ConstStrings/GoWinSDR/Firmware/GoWinSDR_STM32/Hardware/ad9361/command.c

/**************************************************************************//**
 *   @file   command.c
 *   @brief  Implementation of AD9361 Command Driver.
 *   @author DBogdan (dragos.bogdan@analog.com)
 *******************************************************************************
 * Copyright 2013(c) Analog Devices, Inc.
 *
 * All rights reserved.
 *
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
 * THIS SOFTWARE IS PROVIDED BY ANALOG DEVICES "AS IS" AND ANY EXPRESS OR
 * IMPLIED WARRANTIES, INCLUDING, BUT NOT LIMITED TO, NON-INFRINGEMENT,
 * MERCHANTABILITY AND FITNESS FOR A PARTICULAR PURPOSE ARE DISCLAIMED.
 * IN NO EVENT SHALL ANALOG DEVICES BE LIABLE FOR ANY DIRECT, INDIRECT,
 * INCIDENTAL, SPECIAL, EXEMPLARY, OR CONSEQUENTIAL DAMAGES (INCLUDING, BUT NOT
 * LIMITED TO, INTELLECTUAL PROPERTY RIGHTS, PROCUREMENT OF SUBSTITUTE GOODS OR
 * SERVICES; LOSS OF USE, DATA, OR PROFITS; OR BUSINESS INTERRUPTION) HOWEVER
 * CAUSED AND ON ANY THEORY OF LIABILITY, WHETHER IN CONTRACT, STRICT LIABILITY,
 * OR TORT (INCLUDING NEGLIGENCE OR OTHERWISE) ARISING IN ANY WAY OUT OF THE USE
 * OF THIS SOFTWARE, EVEN IF ADVISED OF THE POSSIBILITY OF SUCH DAMAGE.
*******************************************************************************/

/******************************************************************************/
/***************************** Include Files **********************************/
/******************************************************************************/
#include "command.h"
#include "console.h"
#include "ad9361_api.h"
#include "dac_core.h"
#include "com_fpga.h"

/******************************************************************************/
/************************ Constants Definitions *******************************/
/******************************************************************************/
command cmd_list[] = {
	{"help?", "Displays all available commands.", "", get_help},
	{"register?", "Gets the specified register value.", "", get_register},
	{"tx_lo_freq?", "Gets current TX LO frequency [MHz].", "", get_tx_lo_freq},
	{"tx_lo_freq=", "Sets the TX LO frequency [MHz].", "", set_tx_lo_freq},
	{"tx_samp_freq?", "Gets current TX sampling frequency [Hz].", "", get_tx_samp_freq},
	{"tx_samp_freq=", "Sets the TX sampling frequency [Hz].", "", set_tx_samp_freq},
	{"tx_rf_bandwidth?", "Gets current TX RF bandwidth [Hz].", "", get_tx_rf_bandwidth},
	{"tx_rf_bandwidth=", "Sets the TX RF bandwidth [Hz].", "", set_tx_rf_bandwidth},
	{"tx1_attenuation?", "Gets current TX1 attenuation [mdB].", "", get_tx1_attenuation},
	{"tx1_attenuation=", "Sets the TX1 attenuation [mdB].", "", set_tx1_attenuation},
	{"tx2_attenuation?", "Gets current TX2 attenuation [mdB].", "", get_tx2_attenuation},
	{"tx2_attenuation=", "Sets the TX2 attenuation [mdB].", "", set_tx2_attenuation},
	{"tx_fir_en?", "Gets current TX FIR state.", "", get_tx_fir_en},
	{"tx_fir_en=", "Sets the TX FIR state.", "", set_tx_fir_en},
	{"rx_lo_freq?", "Gets current RX LO frequency [MHz].", "", get_rx_lo_freq},
	{"rx_lo_freq=", "Sets the RX LO frequency [MHz].", "", set_rx_lo_freq},
	{"rx_samp_freq?", "Gets current RX sampling frequency [Hz].", "", get_rx_samp_freq},
	{"rx_samp_freq=", "Sets the RX sampling frequency [Hz].", "", set_rx_samp_freq},
	{"rx_rf_bandwidth?", "Gets current RX RF bandwidth [Hz].", "", get_rx_rf_bandwidth},
	{"rx_rf_bandwidth=", "Sets the RX RF bandwidth [Hz].", "", set_rx_rf_bandwidth},
	{"rx1_gc_mode?", "Gets current RX1 GC mode.", "", get_rx1_gc_mode},
	{"rx1_gc_mode=", "Sets the RX1 GC mode.", "", set_rx1_gc_mode},
	{"rx2_gc_mode?", "Gets current RX2 GC mode.", "", get_rx2_gc_mode},
	{"rx2_gc_mode=", "Sets the RX2 GC mode.", "", set_rx2_gc_mode},
	{"rx1_rf_gain?", "Gets current RX1 RF gain.", "", get_rx1_rf_gain},
	{"rx1_rf_gain=", "Sets the RX1 RF gain.", "", set_rx1_rf_gain},
	{"rx2_rf_gain?", "Gets current RX2 RF gain.", "", get_rx2_rf_gain},
	{"rx2_rf_gain=", "Sets the RX2 RF gain.", "", set_rx2_rf_gain},
	{"rx_fir_en?", "Gets current RX FIR state.", "", get_rx_fir_en},
	{"rx_fir_en=", "Sets the RX FIR state.", "", set_rx_fir_en},
	{"dds_tx1_tone1_freq?", "Gets current DDS TX1 Tone 1 frequency [Hz].", "", get_dds_tx1_tone1_freq},
	{"dds_tx1_tone1_freq=", "Sets the DDS TX1 Tone 1 frequency [Hz].", "", set_dds_tx1_tone1_freq},
	{"dds_tx1_tone2_freq?", "Gets current DDS TX1 Tone 2 frequency [Hz].", "", get_dds_tx1_tone2_freq},
	{"dds_tx1_tone2_freq=", "Sets the DDS TX1 Tone 2 frequency [Hz].", "", set_dds_tx1_tone2_freq},
	{"dds_tx1_tone1_phase?", "Gets current DDS TX1 Tone 1 phase [degrees].", "", get_dds_tx1_tone1_phase},
	{"dds_tx1_tone1_phase=", "Sets the DDS TX1 Tone 1 phase [degrees].", "", set_dds_tx1_tone1_phase},
	{"dds_tx1_tone2_phase?", "Gets current DDS TX1 Tone 2 phase [degrees].", "", get_dds_tx1_tone2_phase},
	{"dds_tx1_tone2_phase=", "Sets the DDS TX1 Tone 2 phase [degrees].", "", set_dds_tx1_tone2_phase},
	{"dds_tx1_tone1_scale?", "Gets current DDS TX1 Tone 1 scale.", "", get_dds_tx1_tone1_scale},
	{"dds_tx1_tone1_scale=", "Sets the DDS TX1 Tone 1 scale.", "", set_dds_tx1_tone1_scale},
	{"dds_tx1_tone2_scale?", "Gets current DDS TX1 Tone 2 scale.", "", get_dds_tx1_tone2_scale},
	{"dds_tx1_tone2_scale=", "Sets the DDS TX1 Tone 2 scale.", "", set_dds_tx1_tone2_scale},
	{"dds_tx2_tone1_freq?", "Gets current DDS TX2 Tone 1 frequency [Hz].", "", get_dds_tx2_tone1_freq},
	{"dds_tx2_tone1_freq=", "Sets the DDS TX2 Tone 1 frequency [Hz].", "", set_dds_tx2_tone1_freq},
	{"dds_tx2_tone2_freq?", "Gets current DDS TX2 Tone 2 frequency [Hz].", "", get_dds_tx2_tone2_freq},
	{"dds_tx2_tone2_freq=", "Sets the DDS TX2 Tone 2 frequency [Hz].", "", set_dds_tx2_tone2_freq},
	{"dds_tx2_tone1_phase?", "Gets current DDS TX2 Tone 1 phase [degrees].", "", get_dds_tx2_tone1_phase},
	{"dds_tx2_tone1_phase=", "Sets the DDS TX2 Tone 1 phase [degrees].", "", set_dds_tx2_tone1_phase},
	{"dds_tx2_tone2_phase?", "Gets current DDS TX2 Tone 2 phase [degrees].", "", get_dds_tx2_tone2_phase},
	{"dds_tx2_tone2_phase=", "Sets the DDS TX2 Tone 2 phase [degrees].", "", set_dds_tx2_tone2_phase},
	{"dds_tx2_tone1_scale?", "Gets current DDS TX2 Tone 1 scale.", "", get_dds_tx2_tone1_scale},
	{"dds_tx2_tone1_scale=", "Sets the DDS TX2 Tone 1 scale.", "", set_dds_tx2_tone1_scale},
	{"dds_tx2_tone2_scale?", "Gets current DDS TX2 Tone 2 scale.", "", dds_tx2_tone2_scale},
	{"dds_tx2_tone2_scale=", "Sets the DDS TX2 Tone 2 scale.", "", set_dds_tx2_tone2_scale},
	{"calibration?", "Get Lo Freq diff.","", get_lo_diff},
	{"calibration=", "Calibrate Lo Freq diff.","", cal_lo_diff},
	{"rx_lo_up=", "Increase RX LO frequency.","", rx_lo_up},
	{"rx_lo_down=", "Decrease RX LO frequency.","", rx_lo_down},
	{"query_led_state?", "Decrease RX LO frequency.","", query_led_state},
	{"query_led_state=", "Decrease RX LO frequency.","", query_led_state_set},
	{"query_temp?", "Get Board Temperature.","", query_temp},
	{"fan_state_set=", "Set fan enable.","", fan_state_set},
};
const char cmd_no = (sizeof(cmd_list) / sizeof(command));

/******************************************************************************/
/************************ Variables Definitions *******************************/
/******************************************************************************/
extern struct dds_state dds_st;
extern struct ad9361_rf_phy *ad9361_phy;

/**************************************************************************//***
 * @brief Show the invalid parameter message.
 *
 * @return None.
*******************************************************************************/
void show_invalid_param_message(unsigned char cmd_no)
{
	console_print("Invalid parameter!\n");
	console_print("%s  - %s\n", (char*)cmd_list[cmd_no].name, (char*)cmd_list[cmd_no].description);
	console_print("Example: %s\n", (char*)cmd_list[cmd_no].example);
}

/**************************************************************************//***
 * @brief Displays all available commands.
 *
 * @return None.
*******************************************************************************/
void get_help(double* param, char param_no) // "help?" command
{
	unsigned char display_cmd;

	console_print("Available commands:\n");
	for(display_cmd = 0; display_cmd < cmd_no; display_cmd++)
	{
		console_print("%s  - %s\n", (char*)cmd_list[display_cmd].name,
								  (char*)cmd_list[display_cmd].description);
	}
}

/**************************************************************************//***
 * @brief Displays all available commands.
 *
 * @return None.
*******************************************************************************/
void get_register(double* param, char param_no) // "register?" command
{
	// uint16_t reg_addr;
	// uint8_t reg_val;
	// SPI_HandleTypeDef spi;

	// if(param_no >= 1)
	// {
	// 	spi.id_no = 0;
	// 	reg_addr = param[0];
	// 	reg_val = ad9361_spi_read(&spi, reg_addr);
	// 	console_print("register[0x%x]=0x%x\n", reg_addr, reg_val);
	// }
	// else
	// 	show_invalid_param_message(1);
	console_print("Use empty: command.c::get_register\n");
}

/**************************************************************************//***
 * @brief Gets current TX LO frequency [MHz].
 *
 * @return None.
*******************************************************************************/
void get_tx_lo_freq(double* param, char param_no) // "tx_lo_freq?" command
{
	uint64_t lo_freq_hz;

	ad9361_get_tx_lo_freq(ad9361_phy, &lo_freq_hz);
	lo_freq_hz /= 1000000;
	console_print("tx_lo_freq=%d\n", (uint32_t)lo_freq_hz);
}

/**************************************************************************//***
 * @brief Sets the TX LO frequency [MHz].
 *
 * @return None.
*******************************************************************************/
void set_tx_lo_freq(double* param, char param_no) // "tx_lo_freq=" command
{
	uint64_t lo_freq_hz;

	if(param_no >= 1)
	{
		lo_freq_hz = param[0];
		lo_freq_hz *= 1000000;
		ad9361_set_tx_lo_freq(ad9361_phy, lo_freq_hz);
		lo_freq_hz /= 1000000;
		console_print("tx_lo_freq=%d\n", (uint32_t)lo_freq_hz);
	}
}

/**************************************************************************//***
 * @brief Gets current sampling frequency [Hz].
 *
 * @return None.
*******************************************************************************/
void get_tx_samp_freq(double* param, char param_no) // "tx_samp_freq?" command
{
	uint32_t sampling_freq_hz;

	ad9361_get_tx_sampling_freq(ad9361_phy, &sampling_freq_hz);
	console_print("tx_samp_freq=%d\n", sampling_freq_hz);
}

/**************************************************************************//***
 * @brief Sets the sampling frequency [Hz].
 *
 * @return None.
*******************************************************************************/
void set_tx_samp_freq(double* param, char param_no) // "tx_samp_freq=" command
{
	uint32_t sampling_freq_hz;

	if(param_no >= 1)
	{
		sampling_freq_hz = (uint32_t)param[0];
		ad9361_set_tx_sampling_freq(ad9361_phy, sampling_freq_hz);
		ad9361_get_tx_sampling_freq(ad9361_phy, &sampling_freq_hz);
		dds_update(ad9361_phy);
		console_print("tx_samp_freq=%d\n", sampling_freq_hz);
	}
	else
		show_invalid_param_message(1);
}

/**************************************************************************//***
 * @brief Gets current TX RF bandwidth [Hz].
 *
 * @return None.
*******************************************************************************/
void get_tx_rf_bandwidth(double* param, char param_no) // "tx_rf_bandwidth?" command
{
	uint32_t bandwidth_hz;

	ad9361_get_tx_rf_bandwidth(ad9361_phy, &bandwidth_hz);
	console_print("tx_rf_bandwidth=%d\n", bandwidth_hz);
}

/**************************************************************************//***
 * @brief Sets the TX RF bandwidth [Hz].
 *
 * @return None.
*******************************************************************************/
void set_tx_rf_bandwidth(double* param, char param_no) // "tx_rf_bandwidth=" command
{
	uint32_t bandwidth_hz;

	if(param_no >= 1)
	{
		bandwidth_hz = param[0];
		ad9361_set_tx_rf_bandwidth(ad9361_phy, bandwidth_hz);
	}
	else
		show_invalid_param_message(1);
}

/**************************************************************************//***
 * @brief Gets current TX1 attenuation [mdB].
 *
 * @return None.
*******************************************************************************/
void get_tx1_attenuation(double* param, char param_no) // "tx1_attenuation?" command
{
	uint32_t attenuation_mdb;

	ad9361_get_tx_attenuation(ad9361_phy, 0, &attenuation_mdb);
	console_print("tx1_attenuation=%d\n", attenuation_mdb);
}

/**************************************************************************//***
 * @brief Sets the TX1 attenuation [mdB].
 *
 * @return None.
*******************************************************************************/
void set_tx1_attenuation(double* param, char param_no) // "tx1_attenuation=" command
{
	uint32_t attenuation_mdb;

	if(param_no >= 1)
	{
		attenuation_mdb = param[0];
		ad9361_set_tx_attenuation(ad9361_phy, 0, attenuation_mdb);
		console_print("tx1_attenuation=%d\n", attenuation_mdb);
	}
	else
		show_invalid_param_message(1);
}

/**************************************************************************//***
 * @brief Gets current TX2 attenuation [mdB].
 *
 * @return None.
*******************************************************************************/
void get_tx2_attenuation(double* param, char param_no) // "tx1_attenuation?" command
{
	uint32_t attenuation_mdb;

	ad9361_get_tx_attenuation(ad9361_phy, 1, &attenuation_mdb);
	console_print("tx2_attenuation=%d\n", attenuation_mdb);
}

/**************************************************************************//***
 * @brief Sets the TX2 attenuation [mdB].
 *
 * @return None.
*******************************************************************************/
void set_tx2_attenuation(double* param, char param_no) // "tx1_attenuation=" command
{
	uint32_t attenuation_mdb;

	if(param_no >= 1)
	{
		attenuation_mdb = param[0];
		ad9361_set_tx_attenuation(ad9361_phy, 1, attenuation_mdb);
		console_print("tx2_attenuation=%d\n", attenuation_mdb);
	}
	else
		show_invalid_param_message(1);
}

/**************************************************************************//***
 * @brief Gets current TX FIR state.
 *
 * @return None.
*******************************************************************************/
void get_tx_fir_en(double* param, char param_no) // "tx_fir_en?" command
{
	uint8_t en_dis;

	ad9361_get_tx_fir_en_dis(ad9361_phy, &en_dis);
	console_print("tx_fir_en=%d\n", en_dis);
}

/**************************************************************************//***
 * @brief Sets the TX FIR state.
 *
 * @return None.
*******************************************************************************/
void set_tx_fir_en(double* param, char param_no) // "tx_fir_en=" command
{
	uint8_t en_dis;

	if(param_no >= 1)
	{
		en_dis = param[0];
		ad9361_set_tx_fir_en_dis(ad9361_phy, en_dis);
		console_print("tx_fir_en=%d\n", en_dis);
	}
	else
		show_invalid_param_message(1);
}

/**************************************************************************//***
 * @brief Gets current RX LO frequency [MHz].
 *
 * @return None.
*******************************************************************************/
void get_rx_lo_freq(double* param, char param_no) // "rx_lo_freq?" command
{
	uint64_t lo_freq_hz;

	ad9361_get_rx_lo_freq(ad9361_phy, &lo_freq_hz);
	lo_freq_hz /= 1000000;
	console_print("rx_lo_freq=%d\n", (uint32_t)lo_freq_hz);
}

/**************************************************************************//***
 * @brief Sets the RX LO frequency [MHz].
 *
 * @return None.
*******************************************************************************/
void set_rx_lo_freq(double* param, char param_no) // "rx_lo_freq=" command
{
	uint64_t lo_freq_hz;

	if(param_no >= 1)
	{
		lo_freq_hz = param[0];
		lo_freq_hz *= 1000000;
		ad9361_set_rx_lo_freq(ad9361_phy, lo_freq_hz);
		lo_freq_hz /= 1000000;
		console_print("rx_lo_freq=%d\n", (uint32_t)lo_freq_hz);
	}
}

/**************************************************************************//***
 * @brief Gets current RX sampling frequency [Hz].
 *
 * @return None.
*******************************************************************************/
void get_rx_samp_freq(double* param, char param_no) // "rx_samp_freq?" command
{
	uint32_t sampling_freq_hz;

	ad9361_get_rx_sampling_freq(ad9361_phy, &sampling_freq_hz);
	console_print("rx_samp_freq=%d\n", sampling_freq_hz);
}

/**************************************************************************//***
 * @brief Sets the RX sampling frequency [Hz].
 *
 * @return None.
*******************************************************************************/
void set_rx_samp_freq(double* param, char param_no) // "rx_samp_freq=" command
{
	uint32_t sampling_freq_hz;

	if(param_no >= 1)
	{
		sampling_freq_hz = (uint32_t)param[0];
		ad9361_set_rx_sampling_freq(ad9361_phy, sampling_freq_hz);
		ad9361_get_rx_sampling_freq(ad9361_phy, &sampling_freq_hz);
		dds_update(ad9361_phy);
		console_print("rx_samp_freq=%d\n", sampling_freq_hz);
	}
	else
		show_invalid_param_message(1);
}

/**************************************************************************//***
 * @brief Gets current RX RF bandwidth [Hz].
 *
 * @return None.
*******************************************************************************/
void get_rx_rf_bandwidth(double* param, char param_no) // "rx_rf_bandwidth?" command
{
	uint32_t bandwidth_hz;

	ad9361_get_rx_rf_bandwidth(ad9361_phy, &bandwidth_hz);
	console_print("rx_rf_bandwidth=%d\n", bandwidth_hz);
}

/**************************************************************************//***
 * @brief Sets the RX RF bandwidth [Hz].
 *
 * @return None.
*******************************************************************************/
void set_rx_rf_bandwidth(double* param, char param_no) // "rx_rf_bandwidth=" command
{
	uint32_t bandwidth_hz;

	if(param_no >= 1)
	{
		bandwidth_hz = param[0];
		ad9361_set_rx_rf_bandwidth(ad9361_phy, bandwidth_hz);
		console_print("rx_rf_bandwidth=%d\n", bandwidth_hz);
	}
	else
		show_invalid_param_message(1);
}

/**************************************************************************//***
 * @brief Gets current RX1 GC mode.
 *
 * @return None.
*******************************************************************************/
void get_rx1_gc_mode(double* param, char param_no) // "rx1_gc_mode?" command
{
	uint8_t gc_mode;

	ad9361_get_rx_gain_control_mode(ad9361_phy, 0, &gc_mode);
	console_print("rx1_gc_mode=%d\n", gc_mode);
}

/**************************************************************************//***
 * @brief Sets the RX1 GC mode.
 *
 * @return None.
*******************************************************************************/
void set_rx1_gc_mode(double* param, char param_no) // "rx1_gc_mode=" command
{
	uint8_t gc_mode;

	if(param_no >= 1)
	{
		gc_mode = param[0];
		ad9361_set_rx_gain_control_mode(ad9361_phy, 0, gc_mode);
		console_print("rx1_gc_mode=%d\n", gc_mode);
	}
	else
		show_invalid_param_message(1);
}

/**************************************************************************//***
 * @brief Gets current RX2 GC mode.
 *
 * @return None.
*******************************************************************************/
void get_rx2_gc_mode(double* param, char param_no) // "rx2_gc_mode?" command
{
	uint8_t gc_mode;

	ad9361_get_rx_gain_control_mode(ad9361_phy, 1, &gc_mode);
	console_print("rx2_gc_mode=%d\n", gc_mode);
}

/**************************************************************************//***
 * @brief Sets the RX2 GC mode.
 *
 * @return None.
*******************************************************************************/
void set_rx2_gc_mode(double* param, char param_no) // "rx2_gc_mode=" command
{
	uint8_t gc_mode;

	if(param_no >= 1)
	{
		gc_mode = param[0];
		ad9361_set_rx_gain_control_mode(ad9361_phy, 1, gc_mode);
		console_print("rx2_gc_mode=%d\n", gc_mode);
	}
	else
		show_invalid_param_message(1);
}

/**************************************************************************//***
 * @brief Gets current RX1 RF gain.
 *
 * @return None.
*******************************************************************************/
void get_rx1_rf_gain(double* param, char param_no) // "rx1_rf_gain?" command
{
	int32_t gain_db;

	ad9361_get_rx_rf_gain (ad9361_phy, 0, &gain_db);
	console_print("rx1_rf_gain=%d\n", gain_db);
}

/**************************************************************************//***
 * @brief Sets the RX1 RF gain.
 *
 * @return None.
*******************************************************************************/
void set_rx1_rf_gain(double* param, char param_no) // "rx1_rf_gain=" command
{
	int32_t gain_db;

	if(param_no >= 1)
	{
		gain_db = param[0];
		ad9361_set_rx_rf_gain (ad9361_phy, 0, gain_db);
		console_print("rx1_rf_gain=%d\n", gain_db);
	}
	else
		show_invalid_param_message(1);
}

/**************************************************************************//***
 * @brief Gets current RX2 RF gain.
 *
 * @return None.
*******************************************************************************/
void get_rx2_rf_gain(double* param, char param_no) // "rx2_rf_gain?" command
{
	int32_t gain_db;

	ad9361_get_rx_rf_gain (ad9361_phy, 1, &gain_db);
	console_print("rx2_rf_gain=%d\n", gain_db);
}

/**************************************************************************//***
 * @brief Sets the RX2 RF gain.
 *
 * @return None.
*******************************************************************************/
void set_rx2_rf_gain(double* param, char param_no) // "rx2_rf_gain=" command
{
	int32_t gain_db;

	if(param_no >= 1)
	{
		gain_db = param[0];
		ad9361_set_rx_rf_gain (ad9361_phy, 1, gain_db);
		console_print("rx2_rf_gain=%d\n", gain_db);
	}
	else
		show_invalid_param_message(1);
}

/**************************************************************************//***
 * @brief Gets current RX FIR state.
 *
 * @return None.
*******************************************************************************/
void get_rx_fir_en(double* param, char param_no) // "rx_fir_en?" command
{
	uint8_t en_dis;

	ad9361_get_rx_fir_en_dis(ad9361_phy, &en_dis);
	console_print("rx_fir_en=%d\n", en_dis);
}

/**************************************************************************//***
 * @brief Sets the RX FIR state.
 *
 * @return None.
*******************************************************************************/
void set_rx_fir_en(double* param, char param_no) // "rx_fir_en=" command
{
	uint8_t en_dis;

	if(param_no >= 1)
	{
		en_dis = param[0];
		ad9361_set_rx_fir_en_dis(ad9361_phy, en_dis);
		console_print("rx_fir_en=%d\n", en_dis);
	}
	else
		show_invalid_param_message(1);
}

/**************************************************************************//***
 * @brief Gets current DDS TX1 Tone 1 frequency [Hz].
 *
 * @return None.
*******************************************************************************/
void get_dds_tx1_tone1_freq(double* param, char param_no)	// dds_tx1_tone1_freq?
{
	uint32_t freq = dds_st.cached_freq[DDS_CHAN_TX1_I_F1];

	console_print("dds_tx1_tone1_freq=%d\n", freq);
}

/**************************************************************************//***
 * @brief Sets the DDS TX1 Tone 1 frequency [Hz].
 *
 * @return None.
*******************************************************************************/
void set_dds_tx1_tone1_freq(double* param, char param_no)	// dds_tx1_tone1_freq=
{
	uint32_t freq = (uint32_t)param[0];

	if(param_no >= 1)
	{
		dds_set_frequency(ad9361_phy, DDS_CHAN_TX1_I_F1, freq);
		dds_set_frequency(ad9361_phy, DDS_CHAN_TX1_Q_F1, freq);
		console_print("dds_tx1_tone1_freq=%d\n", freq);
	}
	else
		show_invalid_param_message(1);
}

/**************************************************************************//***
 * @brief Gets current DDS TX1 Tone 2 frequency [Hz].
 *
 * @return None.
*******************************************************************************/
void get_dds_tx1_tone2_freq(double* param, char param_no)	// dds_tx1_tone2_freq?
{
	uint32_t freq = dds_st.cached_freq[DDS_CHAN_TX1_I_F2];

	console_print("dds_tx1_tone2_freq=%d\n", freq);
}

/**************************************************************************//***
 * @brief Sets the DDS TX1 Tone 2 frequency [Hz].
 *
 * @return None.
*******************************************************************************/
void set_dds_tx1_tone2_freq(double* param, char param_no)	// dds_tx1_tone2_freq=
{
	uint32_t freq = (uint32_t)param[0];

	if(param_no >= 1)
	{
		dds_set_frequency(ad9361_phy, DDS_CHAN_TX1_I_F2, freq);
		dds_set_frequency(ad9361_phy, DDS_CHAN_TX1_Q_F2, freq);
		console_print("dds_tx1_tone2_freq=%d\n", freq);
	}
	else
		show_invalid_param_message(1);
}

/**************************************************************************//***
 * @brief Gets current DDS TX1 Tone 1 phase [degrees].
 *
 * @return None.
*******************************************************************************/
void get_dds_tx1_tone1_phase(double* param, char param_no)	// dds_tx1_tone1_phase?
{
	uint32_t phase = dds_st.cached_phase[DDS_CHAN_TX1_I_F1];

	phase /= 1000;
	console_print("dds_tx1_tone1_phase=%d\n", phase);
}

/**************************************************************************//***
 * @brief Sets the DDS TX1 Tone 1 phase [degrees].
 *
 * @return None.
*******************************************************************************/
void set_dds_tx1_tone1_phase(double* param, char param_no)	// dds_tx1_tone1_phase=
{
	int32_t phase = (uint32_t)param[0];

	if(param_no >= 1)
	{
		dds_set_phase(ad9361_phy, DDS_CHAN_TX1_I_F1, (uint32_t)(phase * 1000));
		if ((phase - 90) < 0)
			phase += 360;
		dds_set_phase(ad9361_phy, DDS_CHAN_TX1_Q_F1, (uint32_t)((phase - 90) * 1000));
		phase = dds_st.cached_phase[DDS_CHAN_TX1_I_F1] / 1000;
		console_print("dds_tx1_tone1_phase=%d\n", phase);
	}
	else
		show_invalid_param_message(1);
}

/**************************************************************************//***
 * @brief Gets current DDS TX1 Tone 2 phase [degrees].
 *
 * @return None.
*******************************************************************************/
void get_dds_tx1_tone2_phase(double* param, char param_no)	// dds_tx1_tone2_phase?
{
	uint32_t phase = dds_st.cached_phase[DDS_CHAN_TX1_I_F2];

	phase /= 1000;
	console_print("dds_tx1_tone2_phase=%d\n", phase);
}

/**************************************************************************//***
 * @brief Sets the DDS TX1 Tone 2 phase [degrees].
 *
 * @return None.
*******************************************************************************/
void set_dds_tx1_tone2_phase(double* param, char param_no)	// dds_tx1_tone2_phase=
{
	int32_t phase = (uint32_t)param[0];

	if(param_no >= 1)
	{
		dds_set_phase(ad9361_phy, DDS_CHAN_TX1_I_F2, (uint32_t)(phase * 1000));
		if ((phase - 90) < 0)
			phase += 360;
		dds_set_phase(ad9361_phy, DDS_CHAN_TX1_Q_F2, (uint32_t)((phase - 90) * 1000));
		phase = dds_st.cached_phase[DDS_CHAN_TX1_I_F2] / 1000;
		console_print("dds_tx1_tone2_phase=%d\n", phase);
	}
	else
		show_invalid_param_message(1);
}

/**************************************************************************//***
 * @brief Gets current DDS TX1 Tone 1 scale.
 *
 * @return None.
*******************************************************************************/
void get_dds_tx1_tone1_scale(double* param, char param_no)	// dds_tx1_tone1_scale?
{
	int32_t scale = dds_st.cached_scale[DDS_CHAN_TX1_I_F1];

	console_print("dds_tx1_tone1_scale=%d\n", scale);
}

/**************************************************************************//***
 * @brief Sets the DDS TX1 Tone 1 scale.
 *
 * @return None.
*******************************************************************************/
void set_dds_tx1_tone1_scale(double* param, char param_no)	// dds_tx1_tone1_scale=
{
	int32_t scale = (int32_t)param[0];

	if(param_no >= 1)
	{
		dds_set_scale(ad9361_phy, DDS_CHAN_TX1_I_F1, scale);
		dds_set_scale(ad9361_phy, DDS_CHAN_TX1_Q_F1, scale);
		scale = dds_st.cached_scale[DDS_CHAN_TX1_I_F1];
		console_print("dds_tx1_tone1_scale=%d\n", scale);
	}
	else
		show_invalid_param_message(1);
}

/**************************************************************************//***
 * @brief Gets current DDS TX1 Tone 2 scale.
 *
 * @return None.
*******************************************************************************/
void get_dds_tx1_tone2_scale(double* param, char param_no)	// dds_tx1_tone2_scale?
{
	int32_t scale = dds_st.cached_scale[DDS_CHAN_TX1_I_F2];

	console_print("dds_tx1_tone2_scale=%d\n", scale);
}

/**************************************************************************//***
 * @brief Sets the DDS TX1 Tone 2 scale.
 *
 * @return None.
*******************************************************************************/
void set_dds_tx1_tone2_scale(double* param, char param_no)	// dds_tx1_tone2_scale=
{
	int32_t scale = (int32_t)param[0];

	if(param_no >= 1)
	{
		dds_set_scale(ad9361_phy, DDS_CHAN_TX1_I_F2, scale);
		dds_set_scale(ad9361_phy, DDS_CHAN_TX1_Q_F2, scale);
		scale = dds_st.cached_scale[DDS_CHAN_TX1_I_F2];
		console_print("dds_tx1_tone2_scale=%d\n", scale);
	}
	else
		show_invalid_param_message(1);
}

/**************************************************************************//***
 * @brief Gets current DDS TX2 Tone 1 frequency [Hz].
 *
 * @return None.
*******************************************************************************/
void get_dds_tx2_tone1_freq(double* param, char param_no)	// dds_tx2_tone1_freq?
{
	uint32_t freq = dds_st.cached_freq[DDS_CHAN_TX2_I_F1];

	console_print("dds_tx2_tone1_freq=%d\n", freq);
}

/**************************************************************************//***
 * @brief Sets the DDS TX2 Tone 1 frequency [Hz].
 *
 * @return None.
*******************************************************************************/
void set_dds_tx2_tone1_freq(double* param, char param_no)	// dds_tx2_tone1_freq=
{
	uint32_t freq = (uint32_t)param[0];

	if(param_no >= 1)
	{
		dds_set_frequency(ad9361_phy, DDS_CHAN_TX2_I_F1, freq);
		dds_set_frequency(ad9361_phy, DDS_CHAN_TX2_Q_F1, freq);
		console_print("dds_tx2_tone1_freq=%d\n", freq);
	}
	else
		show_invalid_param_message(1);
}

/**************************************************************************//***
 * @brief Gets current DDS TX2 Tone 2 frequency [Hz].
 *
 * @return None.
*******************************************************************************/
void get_dds_tx2_tone2_freq(double* param, char param_no)	// dds_tx2_tone2_freq?
{
	uint32_t freq = dds_st.cached_freq[DDS_CHAN_TX2_I_F2];

	console_print("dds_tx2_tone2_freq=%d\n", freq);
}

/**************************************************************************//***
 * @brief Sets the DDS TX2 Tone 2 frequency [Hz].
 *
 * @return None.
*******************************************************************************/
void set_dds_tx2_tone2_freq(double* param, char param_no)	// dds_tx2_tone2_freq=
{
	uint32_t freq = (uint32_t)param[0];

	if(param_no >= 1)
	{
		dds_set_frequency(ad9361_phy, DDS_CHAN_TX2_I_F2, freq);
		dds_set_frequency(ad9361_phy, DDS_CHAN_TX2_Q_F2, freq);
		console_print("dds_tx2_tone2_freq=%d\n", freq);
	}
	else
		show_invalid_param_message(1);
}

/**************************************************************************//***
 * @brief Gets current DDS TX2 Tone 1 phase [degrees].
 *
 * @return None.
*******************************************************************************/
void get_dds_tx2_tone1_phase(double* param, char param_no)	// dds_tx2_tone1_phase?
{
	uint32_t phase = dds_st.cached_phase[DDS_CHAN_TX2_I_F1];

	phase /= 1000;
	console_print("dds_tx2_tone1_phase=%d\n", phase);
}

/**************************************************************************//***
 * @brief Sets the DDS TX2 Tone 1 phase [degrees].
 *
 * @return None.
*******************************************************************************/
void set_dds_tx2_tone1_phase(double* param, char param_no)	// dds_tx2_tone1_phase=
{
	int32_t phase = (uint32_t)param[0];

	if(param_no >= 1)
	{
		dds_set_phase(ad9361_phy, DDS_CHAN_TX2_I_F1, (uint32_t)(phase * 1000));
		if ((phase - 90) < 0)
			phase += 360;
		dds_set_phase(ad9361_phy, DDS_CHAN_TX2_Q_F1, (uint32_t)((phase - 90) * 1000));
		phase = dds_st.cached_phase[DDS_CHAN_TX2_I_F1] / 1000;
		console_print("dds_tx2_tone1_phase=%d\n", phase);
	}
	else
		show_invalid_param_message(1);
}

/**************************************************************************//***
 * @brief Gets current DDS TX2 Tone 2 phase [degrees].
 *
 * @return None.
*******************************************************************************/
void get_dds_tx2_tone2_phase(double* param, char param_no)	// dds_tx2_tone2_phase?
{
	uint32_t phase = dds_st.cached_phase[DDS_CHAN_TX2_I_F2];

	phase /= 1000;
	console_print("dds_tx2_f2_phase=%d\n", phase);
}

/**************************************************************************//***
 * @brief Sets the DDS TX2 Tone 2 phase [degrees].
 *
 * @return None.
*******************************************************************************/
void set_dds_tx2_tone2_phase(double* param, char param_no)	// dds_tx2_tone2_phase=
{
	int32_t phase = (uint32_t)param[0];

	if(param_no >= 1)
	{
		dds_set_phase(ad9361_phy, DDS_CHAN_TX2_I_F2, (uint32_t)(phase * 1000));
		if ((phase - 90) < 0)
			phase += 360;
		dds_set_phase(ad9361_phy, DDS_CHAN_TX2_Q_F2, (uint32_t)((phase - 90) * 1000));
		phase = dds_st.cached_phase[DDS_CHAN_TX2_I_F2] / 1000;
		console_print("dds_tx2_tone2_phase=%d\n", phase);
	}
	else
		show_invalid_param_message(1);
}

/**************************************************************************//***
 * @brief Gets current DDS TX2 Tone 1 scale.
 *
 * @return None.
*******************************************************************************/
void get_dds_tx2_tone1_scale(double* param, char param_no)	// dds_tx2_tone1_scale?
{
	int32_t scale = dds_st.cached_scale[DDS_CHAN_TX2_I_F1];

	console_print("dds_tx2_tone1_scale=%d\n", scale);
}

/**************************************************************************//***
 * @brief Sets the DDS TX2 Tone 1 scale.
 *
 * @return None.
*******************************************************************************/
void set_dds_tx2_tone1_scale(double* param, char param_no)	// dds_tx2_tone1_scale=
{
	int32_t scale = (int32_t)param[0];

	if(param_no >= 1)
	{
		dds_set_scale(ad9361_phy, DDS_CHAN_TX2_I_F1, scale);
		dds_set_scale(ad9361_phy, DDS_CHAN_TX2_Q_F1, scale);
		scale = dds_st.cached_scale[DDS_CHAN_TX2_I_F1];
		console_print("dds_tx2_tone1_scale=%d\n", scale);
	}
	else
		show_invalid_param_message(1);
}

/**************************************************************************//***
 * @brief Gets current DDS TX2 Tone 2 scale.
 *
 * @return None.
*******************************************************************************/
void dds_tx2_tone2_scale(double* param, char param_no)	// dds_tx2_tone2_scale?
{
	int32_t scale = dds_st.cached_scale[DDS_CHAN_TX2_I_F2];

	console_print("dds_tx2_tone2_scale=%d\n", scale);
}

/**************************************************************************//***
 * @brief Sets the DDS TX2 Tone 2 scale.
 *
 * @return None.
*******************************************************************************/
void set_dds_tx2_tone2_scale(double* param, char param_no)	// dds_tx2_tone2_scale=
{
	int32_t scale = (int32_t)param[0];

	if(param_no >= 1)
	{
		dds_set_scale(ad9361_phy, DDS_CHAN_TX2_I_F2, scale);
		dds_set_scale(ad9361_phy, DDS_CHAN_TX2_Q_F2, scale);
		scale = dds_st.cached_scale[DDS_CHAN_TX2_I_F2];
		console_print("dds_tx2_tone2_scale=%d\n", scale);
	}
	else
		show_invalid_param_message(1);
}



void get_lo_diff(double* param, char param_no)
{

	uint32_t freq_err = QueryDataFromFPGA_Polling();
	console_print("Current Frequency Error:%d Hz\n", freq_err);

}

#define Freq_Threshold 20000

void cal_lo_diff(double* param, char param_no)
{
	uint32_t freq_err_sum = 0;
	uint32_t min_val = 0xFFFFFFFF;
	uint32_t max_val = 0;
	uint32_t valid_count = 0;
	for (int i = 0; i < 10; i++){
		HAL_Delay(1000);
		uint32_t freq_err = QueryDataFromFPGA_Polling();
		console_print("[Calibration]::Current Frequency Error:%d Hz\n", freq_err);
		
		if (freq_err > Freq_Threshold)
		{
			continue;
		}
		valid_count++;
		if (freq_err < min_val) min_val = freq_err;
		if (freq_err > max_val) max_val = freq_err;
		
		freq_err_sum += freq_err;
	}
	if (valid_count < 3)
	{
		return;
	}

	freq_err_sum -= (min_val + max_val);
	freq_err_sum = (freq_err_sum * valid_count) / (valid_count - 2);

	uint32_t freq_err = freq_err_sum / valid_count;
	console_print("[Calibration]::Average Frequency Error:%d Hz\n", freq_err);
	
	if (freq_err > 100000)
	{
		console_print("[Calibration]::Calibration Fail!\n");
		return;
	}

	uint64_t lo_freq_hz;
	ad9361_get_rx_lo_freq(ad9361_phy, &lo_freq_hz);
	console_print("[Calibration]::Current Lo Frequency:%d%d%d Hz\n", (uint32_t)(lo_freq_hz / 1000000000), (uint32_t)((lo_freq_hz % 1000000000) / 1000000), (uint32_t)(lo_freq_hz % 1000000));
	
	uint32_t adj_up_err, adj_down_err;

	ad9361_set_rx_lo_freq(ad9361_phy, lo_freq_hz + freq_err);
	console_print("[Calibration]::Setting Lo Freq to: %d%d%d Hz\n", (uint32_t)((lo_freq_hz + freq_err) / 1000000000), (uint32_t)(((lo_freq_hz + freq_err) % 1000000000) / 1000000), (uint32_t)((lo_freq_hz + freq_err) % 1000000));
	HAL_Delay(8000);
	do{
		adj_up_err = QueryDataFromFPGA_Polling();
	} while (adj_up_err > 2 * Freq_Threshold);

	console_print("[Calibration]::Current Frequency Error:%d Hz\n", adj_up_err);
	
	ad9361_set_rx_lo_freq(ad9361_phy, lo_freq_hz - freq_err);
	console_print("[Calibration]::Setting Lo Freq to: %d%d%d Hz\n", (uint32_t)((lo_freq_hz - freq_err) / 1000000000), (uint32_t)(((lo_freq_hz - freq_err) % 1000000000) / 1000000), (uint32_t)((lo_freq_hz - freq_err) % 1000000));
	HAL_Delay(8000);
	do{
		adj_down_err = QueryDataFromFPGA_Polling();
	} while (adj_down_err > 2 * Freq_Threshold);
	console_print("[Calibration]::Current Frequency Error:%d Hz\n", adj_down_err);
	
	if (adj_up_err > freq_err && adj_down_err > freq_err){
		console_print("[Calibration]::Calibration Fail!\n");
	}
	else if (adj_up_err > adj_down_err){
		lo_freq_hz -= freq_err;
		console_print("[Calibration]::Calibration Done!\n");
	}
	else{
		lo_freq_hz += freq_err;
		console_print("[Calibration]::Calibration Done!\n");
	}
	ad9361_set_rx_lo_freq(ad9361_phy, lo_freq_hz);
	console_print("[Calibration]::New Lo Freq:%d%d%d Hz\n", (uint32_t)(lo_freq_hz / 1000000000), (uint32_t)((lo_freq_hz % 1000000000) / 1000000), (uint32_t)(lo_freq_hz % 1000000));
}


void rx_lo_up(double* param, char param_no)
{
	if(param_no >= 1)
	{
		uint64_t lo_freq_hz;
		ad9361_get_rx_lo_freq(ad9361_phy, &lo_freq_hz);
		uint64_t diff = param[0];
		lo_freq_hz += diff;
		ad9361_set_rx_lo_freq(ad9361_phy, lo_freq_hz);
		console_print("New RX LO Frequency:%d%d%d Hz\n", (uint32_t)(lo_freq_hz / 1000000000), (uint32_t)((lo_freq_hz % 1000000000) / 1000000), (uint32_t)(lo_freq_hz % 1000000));
	}
	
}

void rx_lo_down(double* param, char param_no)
{
	if(param_no >= 1)
	{
		uint64_t lo_freq_hz;
		ad9361_get_rx_lo_freq(ad9361_phy, &lo_freq_hz);
		uint64_t diff = param[0];
		lo_freq_hz -= diff;
		ad9361_set_rx_lo_freq(ad9361_phy, lo_freq_hz);
		console_print("New RX LO Frequency:%d%d%d Hz\n", (uint32_t)(lo_freq_hz / 1000000000), (uint32_t)((lo_freq_hz % 1000000000) / 1000000), (uint32_t)(lo_freq_hz % 1000000));
	}
	
}

uint8_t led_state = 0;
uint8_t led_interrupt_en = 0;
uint8_t led_short_lock;
uint8_t led_short_count;
void query_led_state(double *param, char param_no)
{
	console_print("led_state=%d\n", led_state);
}

void query_led_state_set(double* param, char param_no)
{
	if(param_no >= 1)
	{
		uint8_t en = param[0];
		if (en == 1)
		{
			led_interrupt_en = 1;
			HAL_TIM_Base_Start_IT(&htim1);
			console_print("LED Interrupt Enabled\n");
		}
		else
		{
			led_interrupt_en = 0;
			HAL_TIM_Base_Stop_IT(&htim1);
			console_print("LED Interrupt Disabled\n");
		}
	}
}

void query_temp(double* param, char param_no)
{
	uint32_t adc_raw_value = 0;
	float temperature = 0.0f;
	
	HAL_ADC_Start(&hadc1);
    
	if (HAL_ADC_PollForConversion(&hadc1, 100) == HAL_OK)
	{
			adc_raw_value = HAL_ADC_GetValue(&hadc1);
			
			float Vsense = ((float)adc_raw_value * 2.5f) / 4095.0f;
			
			temperature = ((Vsense - 0.76f) / 0.0025f) + 25.0f;
	}
	
	int temp_int = (int)temperature;

	int temp_frac = (int)(temperature * 100) % 100;
	
	HAL_ADC_Stop(&hadc1);
	
	console_print("MCU Temp: %d.%02d C\r\n", temp_int, temp_frac);
	
	uint8_t raw_temp = ad9361_spi_read(ad9361_phy->spi, 0x0E);
	
	temperature = ((float)raw_temp - CALIB_REF_RAW) / 1.14f + CALIB_REF_TEMP;

	temp_int = (int)temperature;
	temp_frac = (int)(temperature * 100) % 100; 
	if (temp_frac < 0) {
			temp_frac = -temp_frac;
	}

	printf("AD9361 Temp: %d.%02d C (Raw: %d)\r\n", temp_int, temp_frac, raw_temp);
}

void fan_state_set(double* param, char param_no)
{
	if(param_no >= 1)
	{
		uint8_t en = param[0];
		if (en == 1)
		{
			HAL_GPIO_WritePin(FAN_GPIO_Port, FAN_Pin, GPIO_PIN_SET);
			console_print("FAN ON\n");
		}
		else
		{
			HAL_GPIO_WritePin(FAN_GPIO_Port, FAN_Pin, GPIO_PIN_RESET);
			console_print("FAN OFF\n");
		}
	}
}

uint32_t rise_trig_time = 0;
uint32_t fall_trig_time = 0;
uint8_t edge_dir=0;
void HAL_GPIO_EXTI_Callback(uint16_t GPIO_Pin)
{
	if (GPIO_Pin == GPIO_PIN_9 && led_interrupt_en)
	{
		if (HAL_GPIO_ReadPin(GPIOA, GPIO_PIN_9) == GPIO_PIN_SET)
		{
			rise_trig_time = HAL_GetTick();
			edge_dir = 0;
		}
		else
		{
			fall_trig_time = HAL_GetTick();
			edge_dir = 1;
		}
		
		if (edge_dir == 0){
			if (HAL_GetTick() - rise_trig_time > 20){
				edge_dir = 0;
			}
			return;
		}
			

		if (fall_trig_time - rise_trig_time > 5) 
		{
			led_state = !led_state;
			led_short_lock = led_state;
			// console_print("LED Toggle\n");
		}
		else
		{
			if (led_short_count == 0){
				led_short_lock = led_state;
				// console_print("Short Lock\n");
			}
			led_short_count = 100; 
			// console_print("short\n");
		}
	}
}

void HAL_TIM_PeriodElapsedCallback(TIM_HandleTypeDef *htim)
{
	if (htim->Instance == TIM1)
	{
		if (led_short_count > 0){
			led_short_count--;
			led_state = 1;
		}
		else{
			led_state = led_short_lock;
			// console_print("Back: %d\n", led_state);
		}
	}
}
