ConstStrings/GoWinSDR/Firmware/GoWinSDR_STM32/Hardware/ad9361/command.h

/**************************************************************************//**
 *   @file   command.h
 *   @brief  Header file of AD9361 Command Driver.
 *   @author DBogdan (dragos.bogdan@analog.com)
 *******************************************************************************
 * Copyright 2013(c) Analog Devices, Inc.
 *
 * All rights reserved.
 *
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
 * THIS SOFTWARE IS PROVIDED BY ANALOG DEVICES "AS IS" AND ANY EXPRESS OR
 * IMPLIED WARRANTIES, INCLUDING, BUT NOT LIMITED TO, NON-INFRINGEMENT,
 * MERCHANTABILITY AND FITNESS FOR A PARTICULAR PURPOSE ARE DISCLAIMED.
 * IN NO EVENT SHALL ANALOG DEVICES BE LIABLE FOR ANY DIRECT, INDIRECT,
 * INCIDENTAL, SPECIAL, EXEMPLARY, OR CONSEQUENTIAL DAMAGES (INCLUDING, BUT NOT
 * LIMITED TO, INTELLECTUAL PROPERTY RIGHTS, PROCUREMENT OF SUBSTITUTE GOODS OR
 * SERVICES; LOSS OF USE, DATA, OR PROFITS; OR BUSINESS INTERRUPTION) HOWEVER
 * CAUSED AND ON ANY THEORY OF LIABILITY, WHETHER IN CONTRACT, STRICT LIABILITY,
 * OR TORT (INCLUDING NEGLIGENCE OR OTHERWISE) ARISING IN ANY WAY OUT OF THE USE
 * OF THIS SOFTWARE, EVEN IF ADVISED OF THE POSSIBILITY OF SUCH DAMAGE.
*******************************************************************************/
#ifndef __COMMAND_H__
#define __COMMAND_H__
#include "main.h"
#include "adc.h"
#include "tim.h"
/******************************************************************************/
/********************** Macros and Constants Definitions **********************/
/******************************************************************************/
#define NULL		((void *)0)
#define SUCCESS_AD		0
#define ERROR_AD		-1

#define CONSOLE_COMMANDS

#define CALIB_REF_RAW   58   
#define CALIB_REF_TEMP  60.0f
/******************************************************************************/
/*************************** Types Declarations *******************************/
/******************************************************************************/
typedef void (*cmd_function)(double* param, char param_no);
typedef struct
{
	const char* name;
	const char* description;
	const char* example;
	cmd_function function;
}command;

/******************************************************************************/
/************************ Functions Declarations ******************************/
/******************************************************************************/

/* Displays all available commands. */
void get_help(double* param, char param_no);

/* Gets the specified register value. */
void get_register(double* param, char param_no);

/* Gets current TX LO frequency. */
void get_tx_lo_freq(double* param, char param_no);

/* Sets the TX LO frequency. */
void set_tx_lo_freq(double* param, char param_no);

/* Gets current TX sampling frequency. */
void get_tx_samp_freq(double* param, char param_no);

/* Sets the TX sampling frequency. */
void set_tx_samp_freq(double* param, char param_no);

/* Gets current TX RF bandwidth. */
void get_tx_rf_bandwidth(double* param, char param_no);

/* Sets the TX RF bandwidth. */
void set_tx_rf_bandwidth(double* param, char param_no);

/* Gets current TX1 attenuation. */
void get_tx1_attenuation(double* param, char param_no);

/* Sets the TX1 attenuation. */
void set_tx1_attenuation(double* param, char param_no);

/* Gets current TX2 attenuation. */
void get_tx2_attenuation(double* param, char param_no);

/* Sets the TX2 attenuation. */
void set_tx2_attenuation(double* param, char param_no);

/* Gets current TX FIR state. */
void get_tx_fir_en(double* param, char param_no);

/* Sets the TX FIR state. */
void set_tx_fir_en(double* param, char param_no);

/* Gets current RX LO frequency. */
void get_rx_lo_freq(double* param, char param_no);

/* Sets the RX LO frequency. */
void set_rx_lo_freq(double* param, char param_no);

/* Gets current RX sampling frequency. */
void get_rx_samp_freq(double* param, char param_no);

/* Sets the RX sampling frequency. */
void set_rx_samp_freq(double* param, char param_no);

/* Gets current RX RF bandwidth. */
void get_rx_rf_bandwidth(double* param, char param_no);

/* Sets the RX RF bandwidth. */
void set_rx_rf_bandwidth(double* param, char param_no);

/* Gets current RX1 GC mode. */
void get_rx1_gc_mode(double* param, char param_no);

/* Sets the RX1 GC mode. */
void set_rx1_gc_mode(double* param, char param_no);

/* Gets current RX2 GC mode. */
void get_rx2_gc_mode(double* param, char param_no);

/* Sets the RX2 GC mode. */
void set_rx2_gc_mode(double* param, char param_no);

/* Gets current RX1 RF gain. */
void get_rx1_rf_gain(double* param, char param_no);

/* Sets the RX1 RF gain. */
void set_rx1_rf_gain(double* param, char param_no);

/* Gets current RX2 RF gain. */
void get_rx2_rf_gain(double* param, char param_no);

/* Sets the RX2 RF gain. */
void set_rx2_rf_gain(double* param, char param_no);

/* Gets current RX FIR state. */
void get_rx_fir_en(double* param, char param_no);

/* Sets the RX FIR state. */
void set_rx_fir_en(double* param, char param_no);

/* Gets current DDS TX1 Tone 1 frequency [Hz]. */
void get_dds_tx1_tone1_freq(double* param, char param_no);

/* Sets the DDS TX1 Tone 1 frequency [Hz]. */
void set_dds_tx1_tone1_freq(double* param, char param_no);

/* Gets current DDS TX1 Tone 2 frequency [Hz]. */
void get_dds_tx1_tone2_freq(double* param, char param_no);

/* Sets the DDS TX1 Tone 2 frequency [Hz]. */
void set_dds_tx1_tone2_freq(double* param, char param_no);

/* Gets current DDS TX1 Tone 1 phase [degrees]. */
void get_dds_tx1_tone1_phase(double* param, char param_no);

/* Sets the DDS TX1 Tone 1 phase [degrees]. */
void set_dds_tx1_tone1_phase(double* param, char param_no);

/* Gets current DDS TX1 Tone 2 phase [degrees]. */
void get_dds_tx1_tone2_phase(double* param, char param_no);

/* Sets the DDS TX1 Tone 2 phase [degrees]. */
void set_dds_tx1_tone2_phase(double* param, char param_no);

/* Gets current DDS TX1 Tone 1 scale. */
void get_dds_tx1_tone1_scale(double* param, char param_no);

/* Sets the DDS TX1 Tone 1 scale. */
void set_dds_tx1_tone1_scale(double* param, char param_no);

/* Gets current DDS TX1 Tone 2 scale. */
void get_dds_tx1_tone2_scale(double* param, char param_no);

/* Sets the DDS TX1 Tone 2 scale. */
void set_dds_tx1_tone2_scale(double* param, char param_no);

/* Gets current DDS TX2 Tone 1 frequency [Hz]. */
void get_dds_tx2_tone1_freq(double* param, char param_no);

/* Sets the DDS TX2 Tone 1 frequency [Hz]. */
void set_dds_tx2_tone1_freq(double* param, char param_no);

/* Gets current DDS TX2 Tone 2 frequency [Hz]. */
void get_dds_tx2_tone2_freq(double* param, char param_no);

/* Sets the DDS TX2 Tone 2 frequency [Hz]. */
void set_dds_tx2_tone2_freq(double* param, char param_no);

/* Gets current DDS TX2 Tone 1 phase [degrees]. */
void get_dds_tx2_tone1_phase(double* param, char param_no);

/* Sets the DDS TX2 Tone 1 phase [degrees]. */
void set_dds_tx2_tone1_phase(double* param, char param_no);

/* Gets current DDS TX2 Tone 2 phase [degrees]. */
void get_dds_tx2_tone2_phase(double* param, char param_no);

/* Sets the DDS TX2 Tone 2 phase [degrees]. */
void set_dds_tx2_tone2_phase(double* param, char param_no);

/* Gets current DDS TX2 Tone 1 scale. */
void get_dds_tx2_tone1_scale(double* param, char param_no);

/* Sets the DDS TX2 Tone 1 scale. */
void set_dds_tx2_tone1_scale(double* param, char param_no);

/* Gets current DDS TX2 Tone 2 scale. */
void dds_tx2_tone2_scale(double* param, char param_no);

/* Sets the DDS TX2 Tone 2 scale. */
void set_dds_tx2_tone2_scale(double* param, char param_no);

void get_lo_diff(double* param, char param_no);

void cal_lo_diff(double* param, char param_no);

void rx_lo_up(double* param, char param_no);

void rx_lo_down(double* param, char param_no);

void query_led_state(double* param, char param_no);

void query_led_state_set(double* param, char param_no);

void query_temp(double* param, char param_no);

void fan_state_set(double* param, char param_no);;

void HAL_GPIO_EXTI_Callback(uint16_t GPIO_Pin);

#endif  // __COMMAND_H__
